remidavidkoster/Redako-AES17-Class-D-Filter/Documentation/2022-12-19_20-24-07.jpg

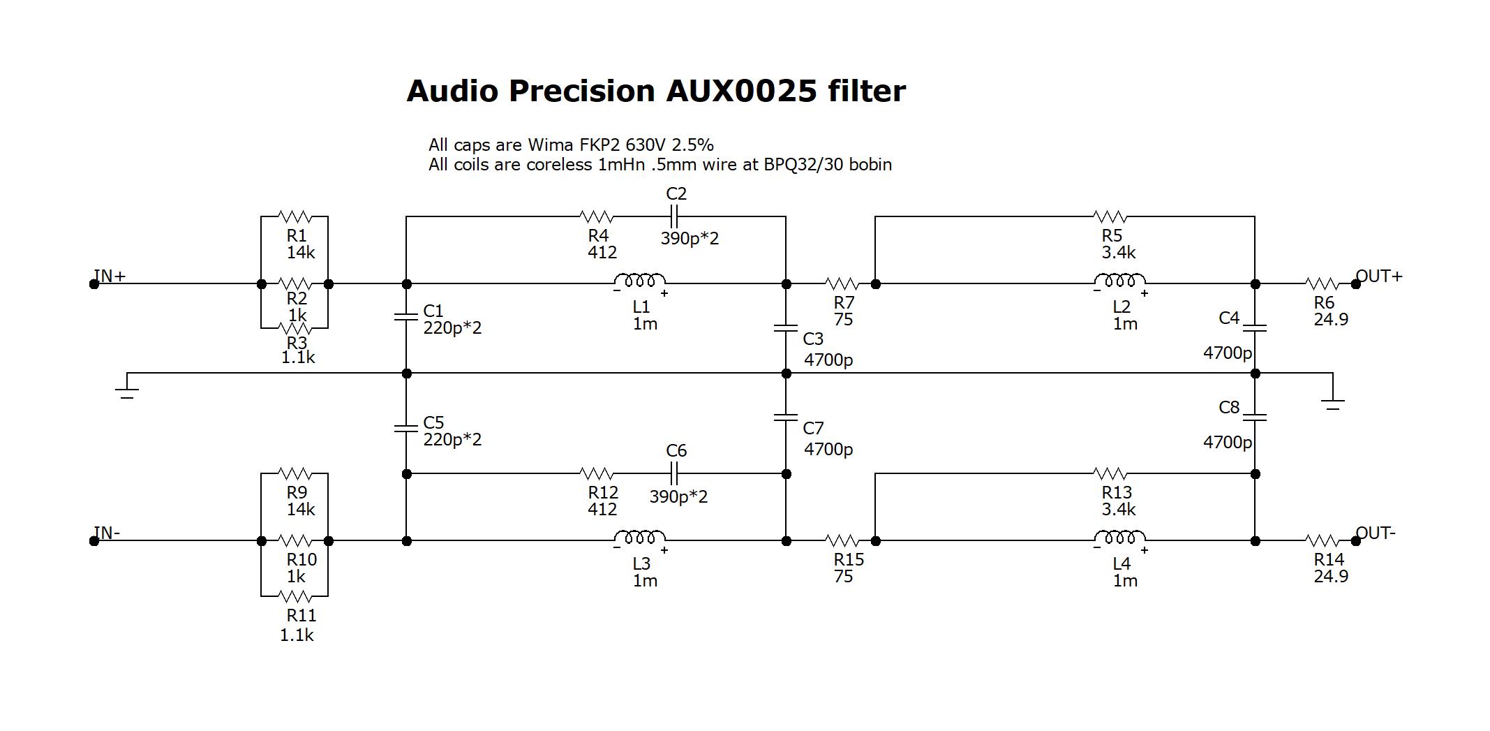
Documentation/2022-12-19_20-24-07.jpg
