remidavidkoster/Redako-AES17-Class-D-Filter/Images/image-20250206095506087.png

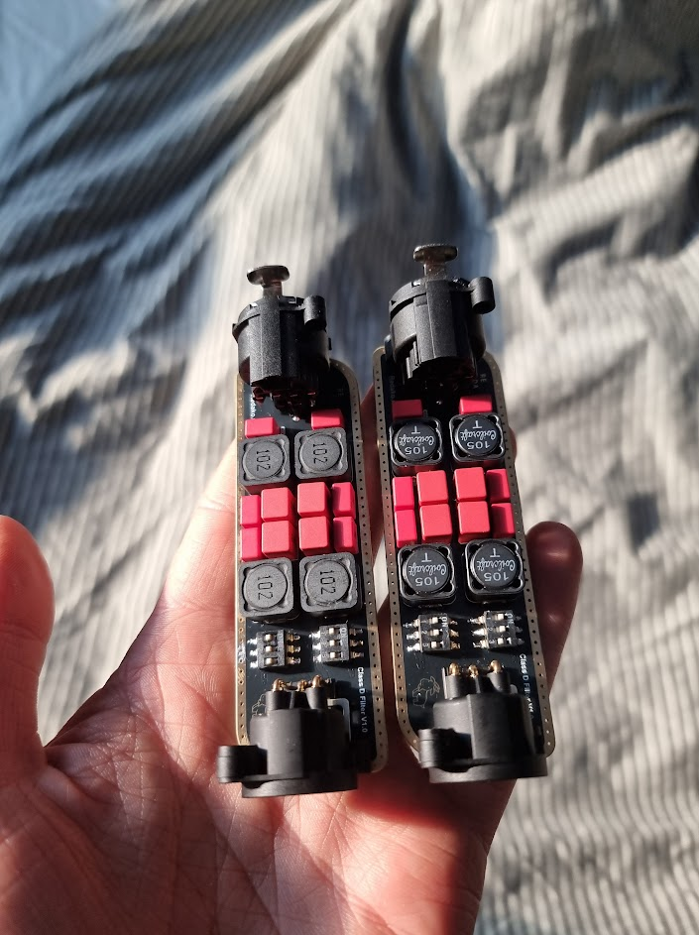
Images/image-20250206095506087.png
