remidavidkoster/Redako-AES17-Class-D-Filter/Simulation/AES17Filter Frequency Domain.asc

C1: cap; 470p
C2: cap; 940p
C3: cap; 4.7n
C4: cap; 4.7n
L1: ind; 1m; Rser=1.4
L2: ind; 1m; Rser=1.4
R1: res; 1k
R2: res; 4k7
R3: res; 3300
R4: res; 20k
R5: res; 390
R6: res; 6k
R7: res; 22
R8: res; 510
R9: res; 75
V1: signal; SINE(0 0.1 1K); AC 1
Named nets: 0
.ac dec 100 1 1meg
"AES17" Filter
ADC
